PaulKennett/LeafRange/Logisoso_compact30pt7b.h

const uint8_t Logisoso_compact30pt7bBitmaps[] PROGMEM = {
  0x00, 0x00, 0x00, 0x00, 0x00, 0x1E, 0x01, 0xFB, 0xFC, 0x0F, 0x9F, 0xE0,
  0x7D, 0xFF, 0x87, 0xEF, 0x3C, 0x3E, 0x79, 0xE3, 0xF3, 0xFF, 0x1F, 0x0F,
  0xF0, 0xF8, 0x7F, 0x8F, 0xC0, 0xF0, 0x7C, 0x00, 0x03, 0xE0, 0x00, 0x3F,
  0x00, 0x01, 0xF0, 0x00, 0x1F, 0x80, 0x00, 0xF8, 0x00, 0x07, 0xC0, 0x00,
  0x7E, 0x00, 0x03, 0xE0, 0x00, 0x3F, 0x00, 0x01, 0xF0, 0x00, 0x0F, 0x80,
  0x00, 0xFC, 0x00, 0x07, 0xC0, 0x00, 0x3E, 0x00, 0x03, 0xE0, 0x00, 0x1F,
  0x00, 0x01, 0xF8, 0x00, 0x0F, 0x80, 0x00, 0x7C, 0x00, 0x07, 0xE0, 0x00,
  0x3E, 0x00, 0x01, 0xF0, 0xF8, 0x1F, 0x0F, 0xE0, 0xF8, 0xFF, 0x8F, 0xCF,
  0xFE, 0x7C, 0x78, 0xF3, 0xE3, 0xC7, 0xBE, 0x1F, 0xFD, 0xF0, 0x7F, 0xCF,
  0x81, 0xFC, 0xF8, 0x07, 0xC0, 0x00, 0x00, 0x00, 0x00, 0x00, 0x00, 0x00,
  0xFF, 0xFF, 0xFF, 0xFF, 0xFF, 0xFF, 0xFF, 0xFF, 0xFF, 0xFF, 0x77, 0xFF,
  0xF7, 0x00, 0x00, 0x01, 0xF8, 0x00, 0x7F, 0xE0, 0x1F, 0xFF, 0x83, 0xFF,
  0xFC, 0x3F, 0xFF, 0xC7, 0xF0, 0xFE, 0x7E, 0x03, 0xEF, 0xC0, 0x3F, 0xF8,
  0x01, 0xFF, 0x80, 0x1F, 0xF8, 0x01, 0xFF, 0x80, 0x1F, 0xF8, 0x01, 0xFF,
  0x80, 0x1F, 0xF8, 0x01, 0xFF, 0x80, 0x1F, 0xF8, 0x01, 0xFF, 0x80, 0x1F,
  0xF8, 0x01, 0xFF, 0x80, 0x1F, 0xF8, 0x01, 0xFF, 0x80, 0x1F, 0xF8, 0x01,
  0xFF, 0x80, 0x1F, 0xF8, 0x01, 0xFF, 0x80, 0x1F, 0xF8, 0x01, 0xFF, 0x80,
  0x1F, 0xF8, 0x01, 0xFF, 0x80, 0x1F, 0xF8, 0x01, 0xFF, 0x80, 0x1F, 0xF8,
  0x01, 0xFF, 0xC0, 0x3F, 0x7C, 0x03, 0xE7, 0xF0, 0xFE, 0x3F, 0xFF, 0xC3,
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
  {  1146,   1,   1,  59,    0,    0 },   // 0x46 'F'
  {  1147,   1,   1,  59,    0,    0 },   // 0x47 'G'
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

const GFXfont Logisoso_compact30pt7b PROGMEM = {
  (uint8_t  *)Logisoso_compact30pt7bBitmaps,
  (GFXglyph *)Logisoso_compact30pt7bGlyphs,
  0x20, 0x7E, 66 };

// Approx. 2649 bytes
