PaulKennett/LeafRange/Logisoso_reduced11pt7b.h

const uint8_t Logisoso_reduced11pt7bBitmaps[] PROGMEM = {
  0x00, 0x00, 0x00, 0x00, 0x00, 0x62, 0xF6, 0xF6, 0x6C, 0x0C, 0x0C, 0x18,
  0x18, 0x18, 0x30, 0x30, 0x30, 0x66, 0x6E, 0x6E, 0xC6, 0x00, 0x00, 0x00,
  0x00, 0x00, 0x00, 0xF4, 0xFF, 0xF0, 0xF0, 0x06, 0x0C, 0x18, 0x60, 0xC1,
  0x86, 0x0C, 0x18, 0x60, 0xC1, 0x86, 0x0C, 0x18, 0x60, 0x3C, 0x7E, 0xE7,
  0xC3, 0xC3, 0xC3, 0xC3, 0xC3, 0xC3, 0xC3, 0xC3, 0xC3, 0xC3, 0xE7, 0x7E,
  0x3C, 0x33, 0xFF, 0xB3, 0x33, 0x33, 0x33, 0x33, 0x33, 0x3C, 0x7E, 0xE7,
  0xC3, 0xC3, 0xC7, 0x06, 0x0E, 0x1C, 0x18, 0x38, 0x30, 0x70, 0xE0, 0xFF,
  0xFF, 0xFF, 0xFF, 0x07, 0x06, 0x0C, 0x1C, 0x1C, 0x1E, 0x07, 0x03, 0x03,
  0x03, 0x03, 0xE7, 0x7E, 0x3C, 0x18, 0x38, 0x30, 0x30, 0x30, 0x70, 0x60,
  0x60, 0x6C, 0xEC, 0xCC, 0xFF, 0xFF, 0x0C, 0x0C, 0x0C, 0xFF, 0xFF, 0xC0,
  0xC0, 0xC0, 0xFC, 0xFE, 0xE7, 0xC3, 0x03, 0x03, 0x03, 0xC3, 0xE7, 0x7E,
  0x3C, 0x3C, 0x7E, 0xE7, 0xC3, 0xC0, 0xC0, 0xFC, 0xFE, 0xE7, 0xC3, 0xC3,
  0xC3, 0xC3, 0xE7, 0x7E, 0x3C, 0xFF, 0xFF, 0xC6, 0xC6, 0x06, 0x06, 0x0C,
  0x0C, 0x0C, 0x0C, 0x18, 0x18, 0x18, 0x18, 0x30, 0x30, 0x3C, 0x7E, 0xE7,
  0xC3, 0xC3, 0xC3, 0xE7, 0x7E, 0x7E, 0xE7, 0xC3, 0xC3, 0xC3, 0xE7, 0x7E,
  0x3C, 0x3C, 0x7E, 0xE7, 0xC3, 0xC3, 0xC3, 0xC3, 0xE7, 0x7F, 0x3F, 0x03,
  0x03, 0xC3, 0xE7, 0x7E, 0x3C, 0xF0, 0x03, 0xC0, 0x00, 0x00, 0x00, 0x00,
  0x00, 0x0F, 0x81, 0xFF, 0x1E, 0x18, 0xC0, 0x6E, 0x7D, 0xE7, 0xEF, 0x33,
  0x79, 0x9B, 0xCC, 0xDE, 0x66, 0xF3, 0x37, 0x99, 0xBC, 0xCD, 0xE7, 0xFF,
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
  {   316,   8,  16,  10,    1,  -15 },   // 0x46 'F'
  {   332,   8,  16,  10,    1,  -15 },   // 0x47 'G'
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

const GFXfont Logisoso_reduced11pt7b PROGMEM = {
  (uint8_t  *)Logisoso_reduced11pt7bBitmaps,
  (GFXglyph *)Logisoso_reduced11pt7bGlyphs,
  0x20, 0x7E, 24 };

// Approx. 1674 bytes
